exploitagency/ESPager/images/motorola_advisor_remove_block_and_clip_stud_2.jpg

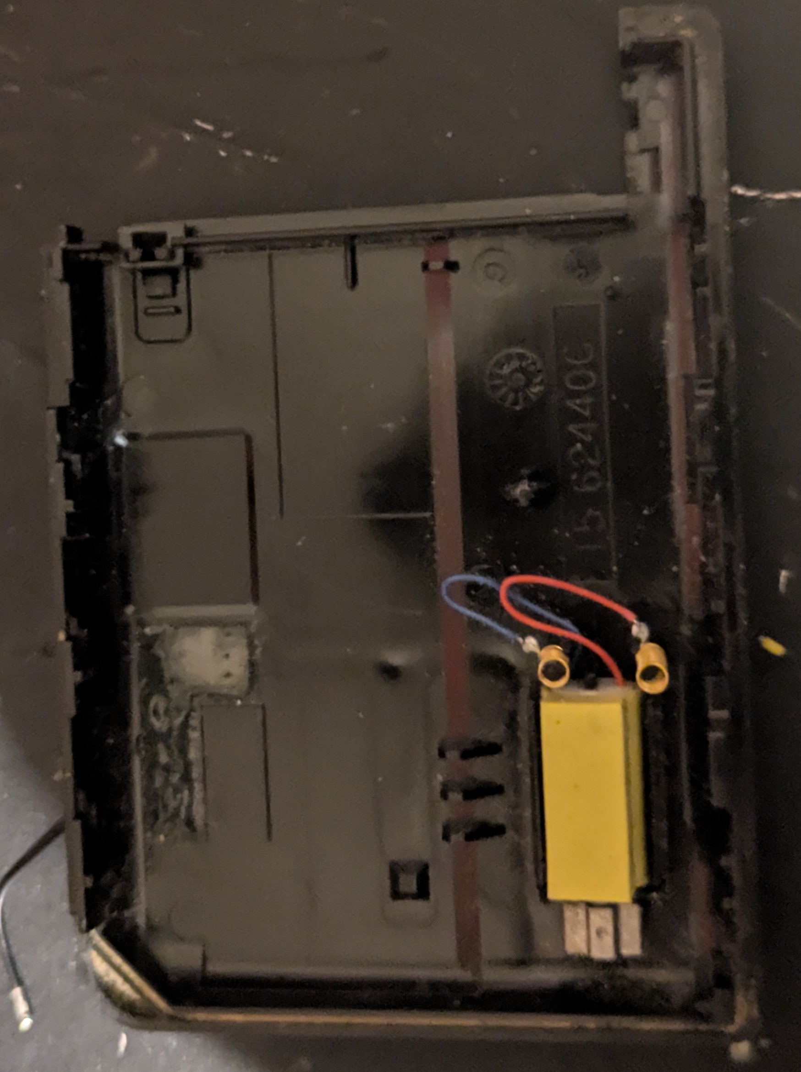
images/motorola_advisor_remove_block_and_clip_stud_2.jpg
