exploitagency/ESPager/pager_ascii_art.h

// ESPager by Hardcore Corey Harding
const char pager_ascii_art[] PROGMEM = R"rawliteral(
<img src="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" alt="" width="226" height="156" />
)rawliteral";
